pjaos/ct6_meter_os/software/server/picow/app1/vga2_bold_16x16.py

WIDTH = 16
HEIGHT = 16
FIRST = 0
LAST = 255
_FONT = \
b'\x00\x00\x00\x00\x00\x00\x00\x00\x00\x00\x00\x00\x00\x00\x00\x00\x00\x00\x00\x00\x00\x00\x00\x00\x00\x00\x00\x00\x00\x00\x00\x00'\
b'\x00\x00\x00\x00\x3f\xfc\x60\x06\xc0\x03\xcc\x33\xc0\x03\xc0\x03\xcf\xf3\xc3\xc3\xc0\x03\x60\x06\x3f\xfc\x00\x00\x00\x00\x00\x00'\
b'\x00\x00\x00\x00\x3f\xfc\x7f\xfe\xff\xff\xf3\xcf\xff\xff\xff\xff\xf0\x0f\xfc\x3f\xff\xff\x7f\xfe\x3f\xfc\x00\x00\x00\x00\x00\x00'\
b'\x00\x00\x00\x00\x00\x00\x1e\x78\x3f\xfc\x7f\xfe\x7f\xfe\x7f\xfe\x3f\xfc\x1f\xf8\x07\xe0\x01\x80\x00\x00\x00\x00\x00\x00\x00\x00'\
b'\x00\x00\x00\x00\x00\x00\x01\x80\x03\xc0\x07\xe0\x0f\xf0\x1f\xf8\x0f\xf0\x07\xe0\x03\xc0\x01\x80\x00\x00\x00\x00\x00\x00\x00\x00'\
b'\x00\x00\x00\x00\x01\xc0\x03\xe0\x03\xe0\x1d\xdc\x3f\xfe\x3f\xfe\x1d\xdc\x01\xc0\x01\xc0\x01\xc0\x07\xf0\x00\x00\x00\x00\x00\x00'\
b'\x00\x00\x00\x00\x01\xc0\x07\xf0\x1f\xfc\x7f\xff\x7f\xff\x7f\xff\x1d\xdc\x01\xc0\x01\xc0\x01\xc0\x07\xf0\x00\x00\x00\x00\x00\x00'\
b'\x00\x00\x00\x00\x00\x00\x00\x00\x00\x00\x00\x00\x03\xc0\x0f\xf0\x0f\xf0\x03\xc0\x00\x00\x00\x00\x00\x00\x00\x00\x00\x00\x00\x00'\
b'\xff\xff\xff\xff\xff\xff\xff\xff\xff\xff\xff\xff\xfc\x3f\xf0\x0f\xf0\x0f\xfc\x3f\xff\xff\xff\xff\xff\xff\xff\xff\xff\xff\xff\xff'\
b'\x00\x00\x00\x00\x00\x00\x00\x00\x00\x00\x0f\xf0\x3c\x3c\x30\x0c\x30\x0c\x3c\x3c\x0f\xf0\x00\x00\x00\x00\x00\x00\x00\x00\x00\x00'\
b'\xff\xff\xff\xff\xff\xff\xff\xff\xff\xff\xf0\x0f\xc3\xc3\xcf\xf3\xcf\xf3\xc3\xc3\xf0\x0f\xff\xff\xff\xff\xff\xff\xff\xff\xff\xff'\
b'\x00\x00\x00\x00\x00\x00\x00\x7f\x00\x1f\x00\x3b\x00\x70\x07\xe0\x1c\x38\x38\x1c\x38\x1c\x1c\x38\x07\xe0\x00\x00\x00\x00\x00\x00'\
b'\x00\x00\x00\x00\x03\xe0\x0e\x38\x1c\x1c\x1c\x1c\x0e\x38\x03\xe0\x01\xc0\x01\xc0\x1f\xfc\x01\xc0\x01\xc0\x00\x00\x00\x00\x00\x00'\
b'\x00\x00\x00\x00\x0f\xff\x0e\x07\x0f\xff\x0e\x00\x0e\x00\x0e\x00\x0e\x00\x0e\x00\x3e\x00\x7e\x00\x3c\x00\x00\x00\x00\x00\x00\x00'\
b'\x00\x00\x00\x00\x1f\xfe\x1c\x0e\x1f\xfe\x1c\x0e\x1c\x0e\x1c\x0e\x1c\x0e\x1c\x0e\x1c\x1e\x3c\x3e\x7c\x1c\x38\x00\x00\x00\x00\x00'\
b'\x00\x00\x00\x00\x00\x00\x01\xc0\x39\xce\x1d\xdc\x0f\xf8\x7e\x3f\x0f\xf8\x1d\xdc\x39\xce\x01\xc0\x00\x00\x00\x00\x00\x00\x00\x00'\
b'\x00\x00\x00\x00\x30\x00\x3c\x00\x3f\x00\x3f\xc0\x3f\xf0\x3f\xfc\x3f\xf0\x3f\xc0\x3f\x00\x3c\x00\x30\x00\x00\x00\x00\x00\x00\x00'\
b'\x00\x00\x00\x00\x00\x0c\x00\x3c\x00\xfc\x03\xfc\x0f\xfc\x3f\xfc\x0f\xfc\x03\xfc\x00\xfc\x00\x3c\x00\x0c\x00\x00\x00\x00\x00\x00'\
b'\x00\x00\x00\x00\x01\xc0\x07\xf0\x1d\xdc\x01\xc0\x01\xc0\x01\xc0\x01\xc0\x01\xc0\x1d\xdc\x07\xf0\x01\xc0\x00\x00\x00\x00\x00\x00'\
b'\x00\x00\x00\x00\x0e\x38\x0e\x38\x0e\x38\x0e\x38\x0e\x38\x0e\x38\x0e\x38\x0e\x38\x00\x00\x0e\x38\x0e\x38\x00\x00\x00\x00\x00\x00'\
b'\x00\x00\x00\x00\x1f\xff\x71\xce\x71\xce\x71\xce\x71\xce\x1f\xce\x01\xce\x01\xce\x01\xce\x01\xce\x01\xce\x00\x00\x00\x00\x00\x00'\
b'\x00\x00\x0f\xf8\x38\x0e\x0e\x00\x03\xe0\x0e\x38\x38\x0e\x38\x0e\x0e\x38\x03\xe0\x00\x38\x38\x0e\x0f\xf8\x00\x00\x00\x00\x00\x00'\
b'\x00\x00\x00\x00\x00\x00\x00\x00\x00\x00\x00\x00\x00\x00\x00\x00\x00\x00\x00\x00\x3f\xff\x3f\xff\x3f\xff\x00\x00\x00\x00\x00\x00'\
b'\x00\x00\x00\x00\x01\xc0\x07\xf0\x1d\xdc\x01\xc0\x01\xc0\x01\xc0\x01\xc0\x01\xc0\x1d\xdc\x07\xf0\x01\xc0\x3f\xfe\x00\x00\x00\x00'\
b'\x00\x00\x00\x00\x01\xc0\x07\xf0\x1d\xdc\x01\xc0\x01\xc0\x01\xc0\x01\xc0\x01\xc0\x01\xc0\x01\xc0\x01\xc0\x00\x00\x00\x00\x00\x00'\
b'\x00\x00\x00\x00\x01\xc0\x01\xc0\x01\xc0\x01\xc0\x01\xc0\x01\xc0\x01\xc0\x01\xc0\x1d\xdc\x07\xf0\x01\xc0\x00\x00\x00\x00\x00\x00'\
b'\x00\x00\x00\x00\x00\x00\x00\x00\x00\x00\x00\x70\x00\x1c\x3f\xff\x00\x1c\x00\x70\x00\x00\x00\x00\x00\x00\x00\x00\x00\x00\x00\x00'\
b'\x00\x00\x00\x00\x00\x00\x00\x00\x00\x00\x03\x80\x0e\x00\x3f\xff\x0e\x00\x03\x80\x00\x00\x00\x00\x00\x00\x00\x00\x00\x00\x00\x00'\
b'\x00\x00\x00\x00\x00\x00\x00\x00\x00\x00\x00\x00\x38\x00\x38\x00\x38\x00\x3f\xff\x00\x00\x00\x00\x00\x00\x00\x00\x00\x00\x00\x00'\
b'\x00\x00\x00\x00\x00\x00\x00\x00\x00\x00\x1c\x38\x38\x1c\x7f\xfe\x38\x1c\x1c\x38\x00\x00\x00\x00\x00\x00\x00\x00\x00\x00\x00\x00'\
b'\x00\x00\x00\x00\x00\x00\x00\x00\x01\x80\x03\xc0\x07\xe0\x0f\xf0\x1f\xf8\x3f\xfc\x7f\xfe\x00\x00\x00\x00\x00\x00\x00\x00\x00\x00'\
b'\x00\x00\x00\x00\x00\x00\x00\x00\x7f\xfe\x3f\xfc\x1f\xf8\x0f\xf0\x07\xe0\x03\xc0\x01\x80\x00\x00\x00\x00\x00\x00\x00\x00\x00\x00'\
b'\x00\x00\x00\x00\x00\x00\x00\x00\x00\x00\x00\x00\x00\x00\x00\x00\x00\x00\x00\x00\x00\x00\x00\x00\x00\x00\x00\x00\x00\x00\x00\x00'\
b'\x00\x00\x00\x00\x01\xc0\x01\xc0\x01\xc0\x01\xc0\x01\xc0\x01\xc0\x01\xc0\x01\xc0\x00\x00\x01\xc0\x01\xc0\x00\x00\x00\x00\x00\x00'\
b'\x00\x00\x1c\x38\x1c\x38\x1c\x38\x1c\x38\x00\x00\x00\x00\x00\x00\x00\x00\x00\x00\x00\x00\x00\x00\x00\x00\x00\x00\x00\x00\x00\x00'\
b'\x00\x00\x00\x00\x00\x00\x1c\x38\x1c\x38\x7f\xfe\x1c\x38\x1c\x38\x1c\x38\x1c\x38\x7f\xfe\x1c\x38\x1c\x38\x00\x00\x00\x00\x00\x00'\
b'\x00\x00\x01\x80\x0f\xf0\x39\x9c\x71\x8e\x71\x80\x39\x80\x0f\xf0\x01\x9c\x01\x8e\x71\x8e\x39\x9c\x0f\xf0\x01\x80\x00\x00\x00\x00'\
b'\x00\x00\x00\x00\x00\x00\x00\x00\x1e\x1c\x1e\x38\x00\x70\x00\xe0\x01\xc0\x03\x80\x07\x00\x0e\x3c\x1c\x3c\x00\x00\x00\x00\x00\x00'\
b'\x00\x00\x00\x00\x07\xc0\x1c\x70\x38\x38\x1c\x70\x07\xc0\x0f\xce\x38\xfc\x70\x78\x70\x78\x38\xfc\x0f\xce\x00\x00\x00\x00\x00\x00'\
b'\x00\x00\x00\xe0\x01\xc0\x03\x80\x07\x00\x00\x00\x00\x00\x00\x00\x00\x00\x00\x00\x00\x00\x00\x00\x00\x00\x00\x00\x00\x00\x00\x00'\
b'\x00\x00\x00\x00\x00\xe0\x01\xc0\x03\x80\x07\x00\x07\x00\x07\x00\x07\x00\x07\x00\x03\x80\x01\xc0\x00\xe0\x00\x00\x00\x00\x00\x00'\
b'\x00\x00\x00\x00\x07\x00\x03\x80\x01\xc0\x00\xe0\x00\xe0\x00\xe0\x00\xe0\x00\xe0\x01\xc0\x03\x80\x07\x00\x00\x00\x00\x00\x00\x00'\
b'\x00\x00\x00\x00\x00\x00\x00\x00\x00\x00\x0e\x38\x03\xe0\x3f\xfe\x03\xe0\x0e\x38\x00\x00\x00\x00\x00\x00\x00\x00\x00\x00\x00\x00'\
b'\x00\x00\x00\x00\x00\x00\x00\x00\x01\xc0\x01\xc0\x01\xc0\x3f\xfe\x01\xc0\x01\xc0\x01\xc0\x00\x00\x00\x00\x00\x00\x00\x00\x00\x00'\
b'\x00\x00\x00\x00\x00\x00\x00\x00\x00\x00\x00\x00\x00\x00\x00\x00\x00\x00\x00\x00\x00\x00\x03\xc0\x03\xc0\x03\x80\x07\x00\x00\x00'\
b'\x00\x00\x00\x00\x00\x00\x00\x00\x00\x00\x00\x00\x00\x00\x3f\xfe\x00\x00\x00\x00\x00\x00\x00\x00\x00\x00\x00\x00\x00\x00\x00\x00'\
b'\x00\x00\x00\x00\x00\x00\x00\x00\x00\x00\x00\x00\x00\x00\x00\x00\x00\x00\x00\x00\x00\x00\x03\xc0\x03\xc0\x00\x00\x00\x00\x00\x00'\
b'\x00\x00\x00\x00\x00\x00\x00\x1c\x00\x38\x00\x70\x00\xe0\x01\xc0\x03\x80\x07\x00\x0e\x00\x1c\x00\x00\x00\x00\x00\x00\x00\x00\x00'\
b'\x00\x00\x00\x00\x07\xe0\x1c\x38\x38\x3c\x38\x7c\x38\xdc\x39\x9c\x3b\x1c\x3e\x1c\x3c\x1c\x1c\x38\x07\xe0\x00\x00\x00\x00\x00\x00'\
b'\x00\x00\x00\x00\x01\xc0\x03\xc0\x0f\xc0\x01\xc0\x01\xc0\x01\xc0\x01\xc0\x01\xc0\x01\xc0\x01\xc0\x01\xc0\x00\x00\x00\x00\x00\x00'\
b'\x00\x00\x00\x00\x0f\xf0\x38\x1c\x00\x0e\x00\x0e\x00\x1c\x00\x70\x01\xc0\x07\x00\x1c\x00\x38\x00\x3f\xfe\x00\x00\x00\x00\x00\x00'\
b'\x00\x00\x00\x00\x0f\xf0\x38\x1c\x00\x0e\x00\x0e\x00\x1c\x01\xf0\x00\x1c\x00\x0e\x00\x0e\x38\x1c\x0f\xf0\x00\x00\x00\x00\x00\x00'\
b'\x00\x00\x00\x00\x01\xf0\x03\xf0\x07\x70\x0e\x70\x1c\x70\x38\x70\x3f\xfc\x00\x70\x00\x70\x00\x70\x00\x70\x00\x00\x00\x00\x00\x00'\
b'\x00\x00\x00\x00\x3f\xfe\x38\x00\x38\x00\x38\x00\x3f\xf0\x00\x1c\x00\x0e\x00\x0e\x00\x0e\x38\x1c\x0f\xf0\x00\x00\x00\x00\x00\x00'\
b'\x00\x00\x00\x00\x07\xf0\x1c\x00\x38\x00\x38\x00\x38\x00\x3f\xf0\x38\x1c\x38\x0e\x38\x0e\x1c\x1c\x07\xf0\x00\x00\x00\x00\x00\x00'\
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
b'\x00\x00\x00\x00\x38\x1c\x38\x1c\x38\x1c\x38\x1c\x38\x1c\x38\x1c\x38\x1c\x1c\x38\x0e\x70\x07\xe0\x03\xc0\x00\x00\x00\x00\x00\x00'\
b'\x00\x00\x00\x00\x70\x0e\x70\x0e\x70\x0e\x70\x0e\x70\x0e\x70\x0e\x71\x8e\x73\xce\x77\xee\x3e\x7c\x1c\x38\x00\x00\x00\x00\x00\x00'\
b'\x00\x00\x00\x00\x38\x1c\x38\x1c\x1c\x38\x0e\x70\x07\xe0\x03\xc0\x07\xe0\x0e\x70\x1c\x38\x38\x1c\x38\x1c\x00\x00\x00\x00\x00\x00'\
b'\x00\x00\x00\x00\x38\x0e\x1c\x1c\x0e\x38\x07\x70\x03\xe0\x01\xc0\x01\xc0\x01\xc0\x01\xc0\x01\xc0\x01\xc0\x00\x00\x00\x00\x00\x00'\
b'\x00\x00\x00\x00\x3f\xfe\x00\x1c\x00\x38\x00\x70\x00\xe0\x01\xc0\x03\x80\x07\x00\x0e\x00\x1c\x00\x3f\xfe\x00\x00\x00\x00\x00\x00'\
b'\x00\x00\x00\x00\x07\xf0\x07\x00\x07\x00\x07\x00\x07\x00\x07\x00\x07\x00\x07\x00\x07\x00\x07\x00\x07\xf0\x00\x00\x00\x00\x00\x00'\
b'\x00\x00\x00\x00\x00\x00\x1c\x00\x0e\x00\x07\x00\x03\x80\x01\xc0\x00\xe0\x00\x70\x00\x38\x00\x1c\x00\x00\x00\x00\x00\x00\x00\x00'\
b'\x00\x00\x00\x00\x07\xf0\x00\x70\x00\x70\x00\x70\x00\x70\x00\x70\x00\x70\x00\x70\x00\x70\x00\x70\x07\xf0\x00\x00\x00\x00\x00\x00'\
b'\x03\xc0\x07\xe0\x0e\x70\x1c\x38\x38\x1c\x00\x00\x00\x00\x00\x00\x00\x00\x00\x00\x00\x00\x00\x00\x00\x00\x00\x00\x00\x00\x00\x00'\
b'\x00\x00\x00\x00\x00\x00\x00\x00\x00\x00\x00\x00\x00\x00\x00\x00\x00\x00\x00\x00\x00\x00\x00\x00\x00\x00\x00\x00\xff\xff\x00\x00'\
b'\x00\x00\x07\x00\x03\x80\x01\xc0\x00\xe0\x00\x00\x00\x00\x00\x00\x00\x00\x00\x00\x00\x00\x00\x00\x00\x00\x00\x00\x00\x00\x00\x00'\
b'\x00\x00\x00\x00\x00\x00\x00\x00\x00\x00\x00\x00\x0f\xf8\x00\x0e\x0f\xfe\x38\x0e\x38\x0e\x38\x0e\x0f\xfe\x00\x00\x00\x00\x00\x00'\
b'\x00\x00\x00\x00\x38\x00\x38\x00\x38\x00\x38\x00\x3f\xf0\x38\x1c\x38\x0e\x38\x0e\x38\x0e\x38\x0e\x3f\xf8\x00\x00\x00\x00\x00\x00'\
b'\x00\x00\x00\x00\x00\x00\x00\x00\x00\x00\x00\x00\x0f\xf8\x38\x0e\x38\x00\x38\x00\x38\x00\x38\x0e\x0f\xf8\x00\x00\x00\x00\x00\x00'\
b'\x00\x00\x00\x00\x00\x0e\x00\x0e\x00\x0e\x00\x0e\x07\xfe\x1c\x0e\x38\x0e\x38\x0e\x38\x0e\x38\x0e\x0f\xfe\x00\x00\x00\x00\x00\x00'\
b'\x00\x00\x00\x00\x00\x00\x00\x00\x00\x00\x00\x00\x0f\xf8\x38\x0e\x38\x0e\x3f\xfe\x38\x00\x38\x00\x0f\xfc\x00\x00\x00\x00\x00\x00'\
b'\x00\x00\x00\x00\x00\xf8\x03\x80\x03\x80\x03\x80\x03\x80\x0f\xf0\x03\x80\x03\x80\x03\x80\x03\x80\x03\x80\x00\x00\x00\x00\x00\x00'\
b'\x00\x00\x00\x00\x00\x00\x00\x00\x00\x00\x00\x00\x0f\xf8\x38\x0e\x38\x0e\x38\x0e\x38\x0e\x0f\xfe\x00\x0e\x00\x0e\x1f\xf8\x00\x00'\
b'\x00\x00\x00\x00\x38\x00\x38\x00\x38\x00\x38\x00\x3b\xf8\x3c\x0e\x38\x0e\x38\x0e\x38\x0e\x38\x0e\x38\x0e\x00\x00\x00\x00\x00\x00'\
b'\x00\x00\x00\x00\x00\x00\x01\xc0\x01\xc0\x00\x00\x01\xc0\x01\xc0\x01\xc0\x01\xc0\x01\xc0\x01\xc0\x01\xc0\x00\x00\x00\x00\x00\x00'\
b'\x00\x00\x00\x00\x00\x00\x00\x70\x00\x70\x00\x00\x00\x70\x00\x70\x00\x70\x00\x70\x00\x70\x00\x70\x00\x70\x00\xe0\x0f\x80\x00\x00'\
b'\x00\x00\x00\x00\x0e\x00\x0e\x00\x0e\x00\x0e\x00\x0e\x38\x0e\x70\x0e\xe0\x0f\xc0\x0e\xe0\x0e\x70\x0e\x38\x00\x00\x00\x00\x00\x00'\
b'\x00\x00\x00\x00\x01\xc0\x01\xc0\x01\xc0\x01\xc0\x01\xc0\x01\xc0\x01\xc0\x01\xc0\x01\xc0\x01\xc0\x01\xc0\x00\x00\x00\x00\x00\x00'\
b'\x00\x00\x00\x00\x00\x00\x00\x00\x00\x00\x00\x00\x3e\x78\x39\xce\x39\xce\x39\xce\x39\xce\x39\xce\x39\xce\x00\x00\x00\x00\x00\x00'\
b'\x00\x00\x00\x00\x00\x00\x00\x00\x00\x00\x00\x00\x3f\xe0\x38\x38\x38\x1c\x38\x1c\x38\x1c\x38\x1c\x38\x1c\x00\x00\x00\x00\x00\x00'\
b'\x00\x00\x00\x00\x00\x00\x00\x00\x00\x00\x00\x00\x07\xf0\x1c\x1c\x38\x0e\x38\x0e\x38\x0e\x1c\x1c\x07\xf0\x00\x00\x00\x00\x00\x00'\
b'\x00\x00\x00\x00\x00\x00\x00\x00\x00\x00\x00\x00\x3f\xf0\x38\x1c\x38\x0e\x38\x0e\x38\x1c\x3f\xf0\x38\x00\x38\x00\x38\x00\x00\x00'\
b'\x00\x00\x00\x00\x00\x00\x00\x00\x00\x00\x00\x00\x07\xfe\x1c\x0e\x38\x0e\x38\x0e\x1c\x0e\x07\xfe\x00\x0e\x00\x0e\x00\x0e\x00\x00'\
b'\x00\x00\x00\x00\x00\x00\x00\x00\x00\x00\x00\x00\x3f\xf0\x38\x1c\x38\x00\x38\x00\x38\x00\x38\x00\x38\x00\x00\x00\x00\x00\x00\x00'\
b'\x00\x00\x00\x00\x00\x00\x00\x00\x00\x00\x00\x00\x0f\xfc\x38\x00\x38\x00\x0f\xf8\x00\x0e\x00\x0e\x1f\xf8\x00\x00\x00\x00\x00\x00'\
b'\x00\x00\x00\x00\x01\xc0\x01\xc0\x01\xc0\x01\xc0\x1f\xfc\x01\xc0\x01\xc0\x01\xc0\x01\xc0\x01\xc0\x01\xc0\x00\x00\x00\x00\x00\x00'\
b'\x00\x00\x00\x00\x00\x00\x00\x00\x00\x00\x00\x00\x38\x1c\x38\x1c\x38\x1c\x38\x1c\x38\x1c\x38\x1c\x0f\xfc\x00\x00\x00\x00\x00\x00'\
b'\x00\x00\x00\x00\x00\x00\x00\x00\x00\x00\x00\x00\x70\x0e\x38\x1c\x1c\x38\x0e\x70\x07\xe0\x03\xc0\x01\x80\x00\x00\x00\x00\x00\x00'\
b'\x00\x00\x00\x00\x00\x00\x00\x00\x00\x00\x00\x00\x38\x0e\x38\x0e\x38\x0e\x39\xce\x3b\xee\x1f\x7c\x0e\x38\x00\x00\x00\x00\x00\x00'\
b'\x00\x00\x00\x00\x00\x00\x00\x00\x00\x00\x00\x00\x1c\x38\x0e\x70\x07\xe0\x03\xc0\x07\xe0\x0e\x70\x1c\x38\x00\x00\x00\x00\x00\x00'\
b'\x00\x00\x00\x00\x00\x00\x00\x00\x00\x00\x00\x00\x38\x0e\x1c\x1c\x0e\x38\x07\x70\x03\xe0\x01\xc0\x03\x80\x07\x00\x0e\x00\x00\x00'\
b'\x00\x00\x00\x00\x00\x00\x00\x00\x00\x00\x00\x00\x3f\xfe\x00\x1c\x00\x70\x01\xc0\x07\x00\x1c\x00\x3f\xfe\x00\x00\x00\x00\x00\x00'\
b'\x00\x00\x00\x00\x00\xf8\x01\xc0\x03\x80\x03\x80\x03\x80\x1e\x00\x03\x80\x03\x80\x03\x80\x01\xc0\x00\xf8\x00\x00\x00\x00\x00\x00'\
b'\x00\x00\x00\x00\x01\xc0\x01\xc0\x01\xc0\x01\xc0\x01\xc0\x00\x00\x01\xc0\x01\xc0\x01\xc0\x01\xc0\x01\xc0\x00\x00\x00\x00\x00\x00'\
b'\x00\x00\x00\x00\x1f\x00\x03\x80\x01\xc0\x01\xc0\x01\xc0\x00\x78\x01\xc0\x01\xc0\x01\xc0\x03\x80\x1f\x00\x00\x00\x00\x00\x00\x00'\
b'\x00\x00\x00\x00\x07\x9e\x3c\xf0\x00\x00\x00\x00\x00\x00\x00\x00\x00\x00\x00\x00\x00\x00\x00\x00\x00\x00\x00\x00\x00\x00\x00\x00'\
b'\x00\x00\x00\x00\x00\x00\x00\x00\x01\xc0\x07\x70\x1c\x1c\x70\x07\x70\x07\x7f\xff\x00\x00\x00\x00\x00\x00\x00\x00\x00\x00\x00\x00'\
b'\x00\x00\x00\x00\x07\xf8\x1c\x0e\x38\x06\x38\x00\x38\x00\x38\x00\x38\x00\x38\x06\x1c\x0e\x07\xf8\x00\x38\x00\x1c\x0f\xf8\x00\x00'\
b'\x00\x00\x00\x00\x00\x00\x1c\x38\x1c\x38\x00\x00\x38\x1c\x38\x1c\x38\x1c\x38\x1c\x38\x1c\x38\x1c\x0f\xfc\x00\x00\x00\x00\x00\x00'\
b'\x00\x00\x00\x00\x00\x38\x00\xe0\x03\x80\x00\x00\x0f\xf8\x38\x0e\x38\x0e\x3f\xfe\x38\x00\x38\x00\x0f\xfc\x00\x00\x00\x00\x00\x00'\
b'\x00\x00\x00\x00\x01\xc0\x07\x70\x1c\x1c\x00\x00\x0f\xf8\x00\x0e\x0f\xfe\x38\x0e\x38\x0e\x38\x0e\x0f\xfe\x00\x00\x00\x00\x00\x00'\
b'\x00\x00\x00\x00\x00\x00\x1c\x1c\x1c\x1c\x00\x00\x0f\xf8\x00\x0e\x0f\xfe\x38\x0e\x38\x0e\x38\x0e\x0f\xfe\x00\x00\x00\x00\x00\x00'\
b'\x00\x00\x00\x00\x07\x00\x01\xc0\x00\x70\x00\x00\x0f\xf8\x00\x0e\x0f\xfe\x38\x0e\x38\x0e\x38\x0e\x0f\xfe\x00\x00\x00\x00\x00\x00'\
b'\x00\x00\x00\x00\x03\xe0\x0e\x38\x03\xe0\x00\x00\x0f\xf8\x00\x0e\x0f\xfe\x38\x0e\x38\x0e\x38\x0e\x0f\xfe\x00\x00\x00\x00\x00\x00'\
b'\x00\x00\x00\x00\x00\x00\x00\x00\x00\x00\x00\x00\x0f\xf0\x38\x1c\x38\x00\x38\x00\x38\x1c\x0f\xf0\x00\x70\x00\x38\x0f\xf0\x00\x00'\
b'\x00\x00\x00\x00\x01\xc0\x07\x70\x1c\x1c\x00\x00\x0f\xf8\x38\x0e\x38\x0e\x3f\xfe\x38\x00\x38\x00\x0f\xfc\x00\x00\x00\x00\x00\x00'\
b'\x00\x00\x00\x00\x00\x00\x1c\x1c\x1c\x1c\x00\x00\x0f\xf8\x38\x0e\x38\x0e\x3f\xfe\x38\x00\x38\x00\x0f\xfc\x00\x00\x00\x00\x00\x00'\
b'\x00\x00\x00\x00\x07\x00\x01\xc0\x00\x70\x00\x00\x0f\xf8\x38\x0e\x38\x0e\x3f\xfe\x38\x00\x38\x00\x0f\xfc\x00\x00\x00\x00\x00\x00'\
b'\x00\x00\x00\x00\x00\x00\x1c\x1c\x1c\x1c\x00\x00\x01\xc0\x01\xc0\x01\xc0\x01\xc0\x01\xc0\x01\xc0\x01\xc0\x00\x00\x00\x00\x00\x00'\
b'\x00\x00\x00\x00\x01\xc0\x07\x70\x1c\x1c\x00\x00\x01\xc0\x01\xc0\x01\xc0\x01\xc0\x01\xc0\x01\xc0\x01\xc0\x00\x00\x00\x00\x00\x00'\
b'\x00\x00\x00\x00\x0e\x00\x03\x80\x00\xe0\x00\x00\x01\xc0\x01\xc0\x01\xc0\x01\xc0\x01\xc0\x01\xc0\x01\xc0\x00\x00\x00\x00\x00\x00'\
b'\x00\x00\x1c\x38\x1c\x38\x00\x00\x03\xc0\x07\xe0\x0e\x70\x1c\x38\x38\x1c\x3f\xfc\x38\x1c\x38\x1c\x38\x1c\x00\x00\x00\x00\x00\x00'\
b'\x03\xc0\x0e\x70\x03\xc0\x00\x00\x03\xc0\x07\xe0\x0e\x70\x1c\x38\x38\x1c\x3f\xfc\x38\x1c\x38\x1c\x38\x1c\x00\x00\x00\x00\x00\x00'\
b'\x00\x70\x01\xc0\x07\x00\x00\x00\x3f\xfc\x38\x00\x38\x00\x38\x00\x3f\xe0\x38\x00\x38\x00\x38\x00\x3f\xfc\x00\x00\x00\x00\x00\x00'\
b'\x00\x00\x00\x00\x00\x00\x00\x00\x00\x00\x00\x00\x3e\x7e\x03\xc7\x03\xc7\x7f\xfe\xe3\xc0\xe3\xc0\x7f\xff\x00\x00\x00\x00\x00\x00'\
b'\x00\x00\x00\x00\x07\xff\x0e\xe0\x1c\xe0\x38\xe0\x70\xe0\x7f\xfe\x70\xe0\x70\xe0\x70\xe0\x70\xe0\x70\xff\x00\x00\x00\x00\x00\x00'\
b'\x00\x00\x00\x00\x01\xc0\x07\x70\x1c\x1c\x00\x00\x07\xf0\x1c\x1c\x38\x0e\x38\x0e\x38\x0e\x1c\x1c\x07\xf0\x00\x00\x00\x00\x00\x00'\
b'\x00\x00\x00\x00\x00\x00\x1c\x1c\x1c\x1c\x00\x00\x07\xf0\x1c\x1c\x38\x0e\x38\x0e\x38\x0e\x1c\x1c\x07\xf0\x00\x00\x00\x00\x00\x00'\
b'\x00\x00\x00\x00\x07\x00\x01\xc0\x00\x70\x00\x00\x07\xf0\x1c\x1c\x38\x0e\x38\x0e\x38\x0e\x1c\x1c\x07\xf0\x00\x00\x00\x00\x00\x00'\
b'\x00\x00\x00\x00\x03\xc0\x0e\x70\x38\x1c\x00\x00\x38\x1c\x38\x1c\x38\x1c\x38\x1c\x38\x1c\x38\x1c\x0f\xfc\x00\x00\x00\x00\x00\x00'\
b'\x00\x00\x00\x00\x0e\x00\x03\x80\x00\xe0\x00\x00\x38\x1c\x38\x1c\x38\x1c\x38\x1c\x38\x1c\x38\x1c\x0f\xfc\x00\x00\x00\x00\x00\x00'\
b'\x00\x00\x00\x00\x00\x00\x1c\x1c\x1c\x1c\x00\x00\x38\x0e\x1c\x1c\x0e\x38\x07\x70\x03\xe0\x01\xc0\x03\x80\x07\x00\x0e\x00\x00\x00'\
b'\x00\x00\x1c\x1c\x1c\x1c\x00\x00\x07\xf0\x1c\x1c\x38\x0e\x38\x0e\x38\x0e\x38\x0e\x38\x0e\x1c\x1c\x07\xf0\x00\x00\x00\x00\x00\x00'\
b'\x00\x00\x1c\x1c\x1c\x1c\x00\x00\x38\x0e\x38\x0e\x38\x0e\x38\x0e\x38\x0e\x38\x0e\x38\x0e\x1c\x1c\x07\xf0\x00\x00\x00\x00\x00\x00'\
b'\x00\x00\x00\x00\x01\xc0\x01\xc0\x0f\xf8\x38\x0e\x38\x00\x38\x00\x38\x00\x38\x1e\x0f\xf8\x01\xc0\x01\xc0\x00\x00\x00\x00\x00\x00'\
b'\x00\x00\x00\x00\x01\xf0\x07\x1c\x07\x00\x07\x00\x1f\xc0\x07\x00\x07\x00\x07\x00\x07\x00\x3f\x0e\x3f\xf8\x00\x00\x00\x00\x00\x00'\
b'\x00\x00\x00\x00\x38\x0e\x1c\x1c\x0e\x38\x07\x70\x03\xe0\x3f\xfe\x01\xc0\x3f\xfe\x01\xc0\x01\xc0\x01\xc0\x00\x00\x00\x00\x00\x00'\
b'\x00\x00\x00\x00\x7f\x80\x70\xe0\x70\x70\x70\xe0\x7f\x9c\x70\x1c\x70\x7f\x70\x1c\x70\x1c\x70\x1c\x70\x1c\x00\x00\x00\x00\x00\x00'\
b'\x00\x00\x00\x00\x00\x78\x01\xce\x01\xc0\x01\xc0\x01\xc0\x1f\xfc\x01\xc0\x01\xc0\x01\xc0\x01\xc0\x39\xc0\x0f\x00\x00\x00\x00\x00'\
b'\x00\x00\x00\x00\x00\x70\x01\xc0\x07\x00\x00\x00\x0f\xf8\x00\x0e\x0f\xfe\x38\x0e\x38\x0e\x38\x0e\x0f\xfe\x00\x00\x00\x00\x00\x00'\
b'\x00\x00\x00\x00\x00\x70\x01\xc0\x07\x00\x00\x00\x01\xc0\x01\xc0\x01\xc0\x01\xc0\x01\xc0\x01\xc0\x01\xc0\x00\x00\x00\x00\x00\x00'\
b'\x00\x00\x00\x00\x00\x70\x01\xc0\x07\x00\x00\x00\x07\xf0\x1c\x1c\x38\x0e\x38\x0e\x38\x0e\x1c\x1c\x07\xf0\x00\x00\x00\x00\x00\x00'\
b'\x00\x00\x00\x00\x00\x70\x01\xc0\x07\x00\x00\x00\x38\x1c\x38\x1c\x38\x1c\x38\x1c\x38\x1c\x38\x1c\x0f\xfc\x00\x00\x00\x00\x00\x00'\
b'\x00\x00\x00\x00\x00\x00\x07\x9c\x3c\xf0\x00\x00\x3f\xe0\x38\x38\x38\x1c\x38\x1c\x38\x1c\x38\x1c\x38\x1c\x00\x00\x00\x00\x00\x00'\
b'\x00\x00\x07\x9e\x3c\xf0\x00\x00\x3c\x0e\x3e\x0e\x3f\x0e\x3b\x8e\x39\xce\x38\xee\x38\x7e\x38\x3e\x38\x1e\x00\x00\x00\x00\x00\x00'\
b'\x00\x00\x00\x00\x0f\xf0\x38\x70\x38\x70\x0f\xfc\x00\x00\x3f\xfc\x00\x00\x00\x00\x00\x00\x00\x00\x00\x00\x00\x00\x00\x00\x00\x00'\
b'\x00\x00\x00\x00\x0f\xc0\x38\x70\x38\x70\x0f\xc0\x00\x00\x3f\xf0\x00\x00\x00\x00\x00\x00\x00\x00\x00\x00\x00\x00\x00\x00\x00\x00'\
b'\x00\x00\x00\x00\x03\x80\x03\x80\x00\x00\x03\x80\x03\x80\x03\x80\x07\x00\x1c\x00\x38\x1c\x1c\x38\x07\xe0\x00\x00\x00\x00\x00\x00'\
b'\x00\x00\x00\x00\x00\x00\x00\x00\x00\x00\x00\x00\x00\x00\x3f\xff\x38\x00\x38\x00\x38\x00\x00\x00\x00\x00\x00\x00\x00\x00\x00\x00'\
b'\x00\x00\x00\x00\x00\x00\x00\x00\x00\x00\x00\x00\x00\x00\x3f\xff\x00\x07\x00\x07\x00\x07\x00\x00\x00\x00\x00\x00\x00\x00\x00\x00'\
b'\x00\x00\x00\x00\x38\x00\x78\x00\x38\x00\x38\x1c\x38\x70\x01\xc0\x07\x00\x1c\x7c\x70\x0e\x00\x1c\x00\x70\x00\xfe\x00\x00\x00\x00'\
b'\x00\x00\x00\x00\x38\x00\x78\x00\x38\x00\x38\x1c\x38\x70\x01\xc0\x07\x00\x1c\x1c\x70\x7c\x01\xdc\x01\xfe\x00\x1c\x00\x00\x00\x00'\
b'\x00\x00\x00\x00\x01\xc0\x01\xc0\x00\x00\x01\xc0\x01\xc0\x01\xc0\x01\xc0\x01\xc0\x01\xc0\x01\xc0\x01\xc0\x00\x00\x00\x00\x00\x00'\
b'\x00\x00\x00\x00\x00\x00\x00\x00\x00\x00\x03\x8e\x0e\x38\x38\xe0\x0e\x38\x03\x8e\x00\x00\x00\x00\x00\x00\x00\x00\x00\x00\x00\x00'\
b'\x00\x00\x00\x00\x00\x00\x00\x00\x00\x00\x38\xe0\x0e\x38\x03\x8e\x0e\x38\x38\xe0\x00\x00\x00\x00\x00\x00\x00\x00\x00\x00\x00\x00'\
b'\x03\x03\x30\x30\x03\x03\x30\x30\x03\x03\x30\x30\x03\x03\x30\x30\x03\x03\x30\x30\x03\x03\x30\x30\x03\x03\x30\x30\x03\x03\x30\x30'\
b'\x33\x33\xcc\xcc\x33\x33\xcc\xcc\x33\x33\xcc\xcc\x33\x33\xcc\xcc\x33\x33\xcc\xcc\x33\x33\xcc\xcc\x33\x33\xcc\xcc\x33\x33\xcc\xcc'\
b'\xf3\xf3\x3f\x3f\xf3\xf3\x3f\x3f\xf3\xf3\x3f\x3f\xf3\xf3\x3f\x3f\xf3\xf3\x3f\x3f\xf3\xf3\x3f\x3f\xf3\xf3\x3f\x3f\xf3\xf3\x3f\x3f'\
b'\x01\xc0\x01\xc0\x01\xc0\x01\xc0\x01\xc0\x01\xc0\x01\xc0\x01\xc0\x01\xc0\x01\xc0\x01\xc0\x01\xc0\x01\xc0\x01\xc0\x01\xc0\x01\xc0'\
b'\x01\xc0\x01\xc0\x01\xc0\x01\xc0\x01\xc0\x01\xc0\x01\xc0\x01\xc0\xff\xc0\x01\xc0\x01\xc0\x01\xc0\x01\xc0\x01\xc0\x01\xc0\x01\xc0'\
b'\x01\xc0\x01\xc0\x01\xc0\x01\xc0\x01\xc0\x01\xc0\xff\xc0\x01\xc0\xff\xc0\x01\xc0\x01\xc0\x01\xc0\x01\xc0\x01\xc0\x01\xc0\x01\xc0'\
b'\x07\x38\x07\x38\x07\x38\x07\x38\x07\x38\x07\x38\x07\x38\x07\x38\xff\x38\x07\x38\x07\x38\x07\x38\x07\x38\x07\x38\x07\x38\x07\x38'\
b'\x00\x00\x00\x00\x00\x00\x00\x00\x00\x00\x00\x00\x00\x00\x00\x00\xff\xf8\x07\x38\x07\x38\x07\x38\x07\x38\x07\x38\x07\x38\x07\x38'\
b'\x00\x00\x00\x00\x00\x00\x00\x00\x00\x00\x00\x00\xff\xc0\x01\xc0\xff\xc0\x01\xc0\x01\xc0\x01\xc0\x01\xc0\x01\xc0\x01\xc0\x01\xc0'\
b'\x07\x38\x07\x38\x07\x38\x07\x38\x07\x38\x07\x38\xff\x38\x00\x38\xff\x38\x07\x38\x07\x38\x07\x38\x07\x38\x07\x38\x07\x38\x07\x38'\
b'\x07\x38\x07\x38\x07\x38\x07\x38\x07\x38\x07\x38\x07\x38\x07\x38\x07\x38\x07\x38\x07\x38\x07\x38\x07\x38\x07\x38\x07\x38\x07\x38'\
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
b'\x00\x00\x00\x00\x00\x00\x00\x00\x00\x00\x00\x00\x00\x00\x00\x00\x01\xff\x01\xc0\x01\xc0\x01\xc0\x01\xc0\x01\xc0\x01\xc0\x01\xc0'\
b'\xff\xff\xff\xff\xff\xff\xff\xff\xff\xff\xff\xff\xff\xff\xff\xff\xff\xff\xff\xff\xff\xff\xff\xff\xff\xff\xff\xff\xff\xff\xff\xff'\
b'\x00\x00\x00\x00\x00\x00\x00\x00\x00\x00\x00\x00\x00\x00\x00\x00\xff\xff\xff\xff\xff\xff\xff\xff\xff\xff\xff\xff\xff\xff\xff\xff'\
b'\xff\x00\xff\x00\xff\x00\xff\x00\xff\x00\xff\x00\xff\x00\xff\x00\xff\x00\xff\x00\xff\x00\xff\x00\xff\x00\xff\x00\xff\x00\xff\x00'\
b'\x00\xff\x00\xff\x00\xff\x00\xff\x00\xff\x00\xff\x00\xff\x00\xff\x00\xff\x00\xff\x00\xff\x00\xff\x00\xff\x00\xff\x00\xff\x00\xff'\
b'\xff\xff\xff\xff\xff\xff\xff\xff\xff\xff\xff\xff\xff\xff\xff\xff\x00\x00\x00\x00\x00\x00\x00\x00\x00\x00\x00\x00\x00\x00\x00\x00'\
b'\x00\x00\x00\x00\x00\x00\x00\x00\x00\x00\x00\x00\x0f\x0e\x39\xdc\x70\xf8\x70\xf0\x70\xf8\x39\xdc\x0f\x0e\x00\x00\x00\x00\x00\x00'\
b'\x00\x00\x00\x00\x00\x00\x00\x00\x0f\xf8\x38\x0e\x38\x0e\x3f\xf8\x38\x0e\x38\x0e\x3f\xf8\x38\x00\x38\x00\x18\x00\x00\x00\x00\x00'\
b'\x00\x00\x00\x00\x3f\xfe\x38\x0e\x38\x0e\x38\x00\x38\x00\x38\x00\x38\x00\x38\x00\x38\x00\x38\x00\x38\x00\x00\x00\x00\x00\x00\x00'\
b'\x00\x00\x00\x00\x00\x00\x00\x00\x00\x00\x00\x00\x3f\xfe\x0e\x38\x0e\x38\x0e\x38\x0e\x38\x0e\x38\x0e\x38\x00\x00\x00\x00\x00\x00'\
b'\x00\x00\x00\x00\x3f\xfe\x38\x0e\x38\x00\x0e\x00\x03\x80\x00\xe0\x03\x80\x0e\x00\x38\x00\x38\x0e\x3f\xfe\x00\x00\x00\x00\x00\x00'\
b'\x00\x00\x00\x00\x00\x00\x00\x00\x00\x00\x00\x00\x07\xff\x1c\x38\x38\x38\x38\x38\x38\x38\x1c\x70\x07\xc0\x00\x00\x00\x00\x00\x00'\
b'\x00\x00\x00\x00\x00\x00\x00\x00\x00\x00\x0e\x0e\x0e\x0e\x0e\x0e\x0e\x0e\x0e\x1c\x0f\xf0\x0e\x00\x0e\x00\x38\x00\x00\x00\x00\x00'\
b'\x00\x00\x00\x00\x00\x00\x00\x00\x00\x00\x0f\x9e\x3c\xf8\x00\xe0\x00\xe0\x00\xe0\x00\xe0\x00\xe0\x00\xe0\x00\x00\x00\x00\x00\x00'\
b'\x00\x00\x00\x00\x1f\xfc\x01\xc0\x07\xf0\x0e\x38\x1c\x1c\x1c\x1c\x1c\x1c\x0e\x38\x07\xf0\x01\xc0\x1f\xfc\x00\x00\x00\x00\x00\x00'\
b'\x00\x00\x00\x00\x07\xf0\x1c\x1c\x38\x0e\x38\x0e\x38\x0e\x3f\xfe\x38\x0e\x38\x0e\x38\x0e\x1c\x1c\x07\xf0\x00\x00\x00\x00\x00\x00'\
b'\x00\x00\x00\x00\x07\xf0\x1c\x1c\x38\x0e\x38\x0e\x38\x0e\x38\x0e\x1c\x1c\x0e\x38\x0e\x38\x0e\x38\x3e\x3e\x00\x00\x00\x00\x00\x00'\
b'\x00\x00\x00\x00\x03\xf0\x0e\x38\x0e\x00\x03\x80\x00\xe0\x07\xf8\x1c\x1c\x38\x1c\x38\x1c\x1c\x38\x07\xe0\x00\x00\x00\x00\x00\x00'\
b'\x00\x00\x00\x00\x00\x00\x00\x00\x00\x00\x00\x00\x3e\x7c\x73\xce\x73\xce\x73\xce\x3e\x7c\x00\x00\x00\x00\x00\x00\x00\x00\x00\x00'\
b'\x00\x00\x00\x00\x00\x00\x00\x1c\x00\x38\x0f\xf0\x38\xfc\x71\xce\x73\x8e\x3f\x1c\x0f\xf0\x1c\x00\x38\x00\x00\x00\x00\x00\x00\x00'\
b'\x00\x00\x00\x00\x03\xf0\x0e\x00\x38\x00\x38\x00\x38\x00\x3f\xf0\x38\x00\x38\x00\x38\x00\x0e\x00\x03\xf0\x00\x00\x00\x00\x00\x00'\
b'\x00\x00\x00\x00\x00\x00\x07\xf0\x1c\x1c\x38\x0e\x38\x0e\x38\x0e\x38\x0e\x38\x0e\x38\x0e\x38\x0e\x38\x0e\x00\x00\x00\x00\x00\x00'\
b'\x00\x00\x00\x00\x00\x00\x00\x00\x3f\xfe\x00\x00\x00\x00\x3f\xfe\x00\x00\x00\x00\x3f\xfe\x00\x00\x00\x00\x00\x00\x00\x00\x00\x00'\
b'\x00\x00\x00\x00\x00\x00\x01\xc0\x01\xc0\x01\xc0\x3f\xfe\x01\xc0\x01\xc0\x01\xc0\x00\x00\x3f\xfe\x00\x00\x00\x00\x00\x00\x00\x00'\
b'\x00\x00\x00\x00\x00\x00\x0e\x00\x03\x80\x00\xe0\x00\x38\x00\xe0\x03\x80\x0e\x00\x00\x00\x3f\xfc\x00\x00\x00\x00\x00\x00\x00\x00'\
b'\x00\x00\x00\x00\x00\x00\x00\x70\x01\xc0\x07\x00\x1c\x00\x07\x00\x01\xc0\x00\x70\x00\x00\x3f\xfc\x00\x00\x00\x00\x00\x00\x00\x00'\
b'\x00\x00\x00\x00\x00\x7c\x01\xc7\x01\xc7\x01\xc0\x01\xc0\x01\xc0\x01\xc0\x01\xc0\x01\xc0\x01\xc0\x01\xc0\x01\xc0\x01\xc0\x01\xc0'\
b'\x01\xc0\x01\xc0\x01\xc0\x01\xc0\x01\xc0\x01\xc0\x01\xc0\x01\xc0\x01\xc0\x01\xc0\x71\xc0\x71\xc0\x1f\x00\x00\x00\x00\x00\x00\x00'\
b'\x00\x00\x00\x00\x00\x00\x01\xc0\x01\xc0\x00\x00\x00\x00\x3f\xfe\x00\x00\x00\x00\x01\xc0\x01\xc0\x00\x00\x00\x00\x00\x00\x00\x00'\
b'\x00\x00\x00\x00\x00\x00\x00\x00\x00\x00\x07\x9e\x3c\xf0\x00\x00\x07\x9e\x3c\xf0\x00\x00\x00\x00\x00\x00\x00\x00\x00\x00\x00\x00'\
b'\x00\x00\x0f\xc0\x38\x70\x38\x70\x0f\xc0\x00\x00\x00\x00\x00\x00\x00\x00\x00\x00\x00\x00\x00\x00\x00\x00\x00\x00\x00\x00\x00\x00'\
b'\x00\x00\x00\x00\x00\x00\x00\x00\x00\x00\x00\x00\x00\x00\x03\xc0\x03\xc0\x00\x00\x00\x00\x00\x00\x00\x00\x00\x00\x00\x00\x00\x00'\
b'\x00\x00\x00\x00\x00\x00\x00\x00\x00\x00\x00\x00\x00\x00\x00\x00\x01\xc0\x00\x00\x00\x00\x00\x00\x00\x00\x00\x00\x00\x00\x00\x00'\
b'\x00\x00\x00\x7f\x00\x70\x00\x70\x00\x70\x00\x70\x00\x70\x00\x70\xf8\x70\x1c\x70\x07\x70\x01\xf0\x00\x70\x00\x00\x00\x00\x00\x00'\
b'\x00\x00\x7f\x80\x70\xe0\x70\xe0\x70\xe0\x70\xe0\x70\xe0\x70\xe0\x00\x00\x00\x00\x00\x00\x00\x00\x00\x00\x00\x00\x00\x00\x00\x00'\
b'\x00\x00\x3f\x00\xe1\xc0\x01\xc0\x07\x00\x1c\x00\x70\x00\xff\xc0\x00\x00\x00\x00\x00\x00\x00\x00\x00\x00\x00\x00\x00\x00\x00\x00'\
b'\x00\x00\x00\x00\x00\x00\x00\x00\x00\x00\x1f\xf8\x1f\xf8\x1f\xf8\x1f\xf8\x1f\xf8\x1f\xf8\x00\x00\x00\x00\x00\x00\x00\x00\x00\x00'\
b'\x00\x00\x00\x00\x00\x00\x00\x00\x00\x00\x00\x00\x00\x00\x00\x00\x00\x00\x00\x00\x00\x00\x00\x00\x00\x00\x00\x00\x00\x00\x00\x00'

FONT = memoryview(_FONT)
