pjaos/ct6_meter_os/software/server/ct6/ct6_app_gui.py

import itertools
import os
import psutil
import objgraph
import inspect
import copy
import platform
import rich
import json
import sys
import threading
from time import time, sleep

import sqlite3

import pandas as pd

from datetime import datetime
from queue import Queue, Empty

from bokeh.layouts import column, row
from bokeh.models import HoverTool
from bokeh.models import TabPanel, Tabs
from bokeh.models.css import Styles
from bokeh.plotting import figure, ColumnDataSource
from bokeh.palettes import Category20_20

from lib.base_constants import BaseConstants
from lib.config import ConfigBase

from lib.yview import YView

from ct6.gui_base import GUIBase

class GUI(GUIBase):
    """@brief Responsible for providing the GUI dashboard for viewing data from CT6 devices.
              This is provided over a Web interface."""

    META_DATA_ROW               = "META_DATA_ROW"

    META_TABLE_ID_INDEX = 0
    META_TABLE_ASSY_INDEX = 1
    META_TABLE_DEVNAME_INDEX = 2
    META_TABLE_CT1_NAME_INDEX = 3
    META_TABLE_CT2_NAME_INDEX = 4
    META_TABLE_CT3_NAME_INDEX = 5
    META_TABLE_CT4_NAME_INDEX = 6
    META_TABLE_CT5_NAME_INDEX = 7
    META_TABLE_CT6_NAME_INDEX = 8

    def __init__(self, uio, options, config, loginCredentialsFile, db_client):
        """@brief Constructor.
           @param uio A UIO instance responsible for stdout/stdin input output.
           @param options The command line argparse options instance.
           @param config The dash app config.
           @param loginCredentialsFile A file containing the login credentials or None if no server authentication is required.
           @param db_client An instance of SQLite3DBClient."""
        super().__init__(uio,
                         options,
                         config,
                         loginCredentialsFile,
                         config.getAttr(AppConfig.LOCAL_GUI_SERVER_ADDRESS),
                         config.getAttr(AppConfig.LOCAL_GUI_SERVER_PORT),
                         config.getAttr(AppConfig.SERVER_ACCESS_LOG_FILE) )

        self._db_client = db_client
        self._db_dicts = {}

    def _executeSQL(self, conn, cmd):
        """@brief Execute an SQL cmd.
           @param cmd The SQL command.
           @return The response tuple."""
        cursor = conn.cursor()
        self._uio.debug(f"SQL CMD: {cmd}")
        cursor.execute(cmd)
        response_tuple = cursor.fetchall()
        conn.commit()
        cursor.close()
        return response_tuple
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
